smonson78/smonson-disk/mcu-source/rtc.h

#ifndef __RTC_H
#define __RTC_H

#include <stdint.h>

#include "stdutil.h"

#define CLOCK_PORT GPIOD
#define CLOCK_PIN 2

#define MCP7951_READ 0b00010011
#define MCP7951_WRITE 0b00010010

typedef struct {
  uint16_t year;
  uint8_t month;
  uint8_t day;
  uint8_t hour;
  uint8_t minute;
  uint8_t second;
} datetime_t;

void rtc_setup();
void rtc_read(uint8_t addr, uint8_t *dest, uint8_t len);
void rtc_write(uint8_t addr, uint8_t *data, uint8_t len);
void rtc_set(datetime_t *datetime);
void rtc_get(datetime_t *dest);

#endif
