smonson78/smonson-disk/mcu-source/spi.h

#ifndef __SPI_H
#define __SPI_H

#include <stdint.h>
#include "stdutil.h"
#include "debug.h"

#define SPI SPI1

#define SPI_MOSI_PORT GPIOB
#define SPI_MOSI_BIT 5

#define SPI_MISO_PORT GPIOB
#define SPI_MISO_BIT 4

#define SPI_CLK_PORT GPIOB
#define SPI_CLK_BIT 3

void spi_setup();
uint8_t spi_transfer(uint8_t send);
void spi_fast();
void spi_slow();

// Fast inlined SPI transfers
static inline void spi_wait_ready() {
	// Wait for SPI transfer completed
	while (SPI->SR & SPI_SR_BSY) {
	}
}

static inline void spi_start_with_value(uint8_t send)
{
    BYTE_ACCESS(SPI->DR) = send;
}

static inline void spi_start() {
	// Start SPI transfer with dummy value (e.g. for reading)
	spi_start_with_value(0xff);
}

static inline void spi_out_nowait(uint8_t send)
{
	spi_wait_ready();
	BYTE_ACCESS(SPI->DR) = send;
}

static inline uint8_t spi_in_nowait()
{
	// Wait until receiver buffer is not empty
	while (!(SPI->SR & SPI_SR_RXNE)) {
	}

	// Return what was received
	return BYTE_ACCESS(SPI->DR);
}

#endif
